yanataka60/X1_SD/JPEG/CZ-800.JPG

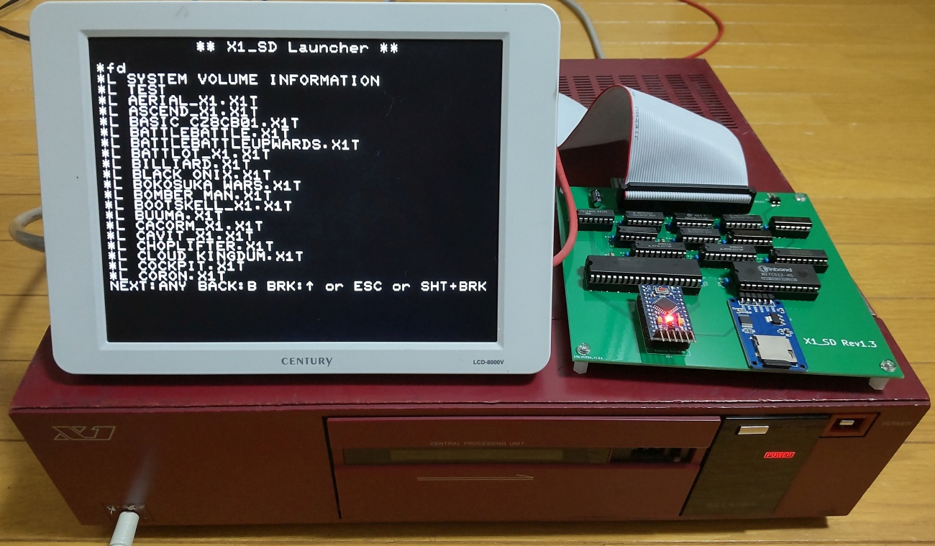
JPEG/CZ-800.JPG
