yanataka60/X1_SD/JPEG/CZ-801.JPG

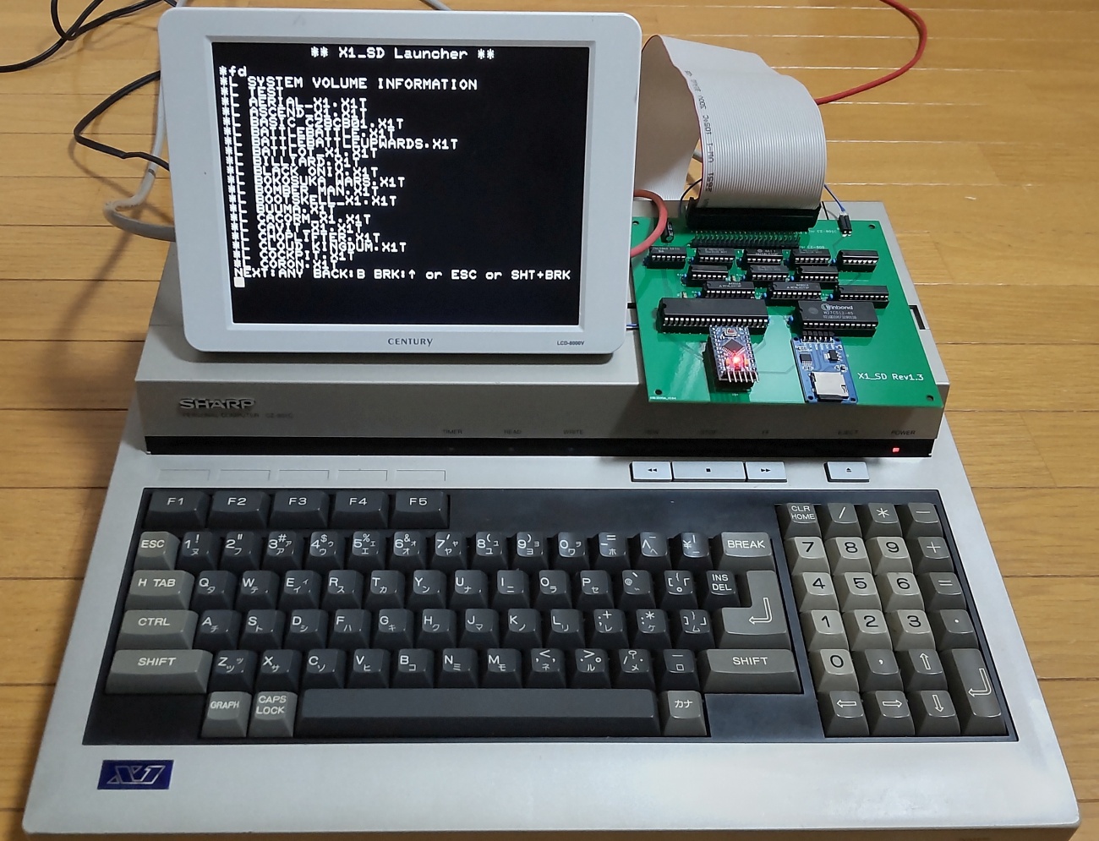
JPEG/CZ-801.JPG
