yanataka60/X1_SD/JPEG/CZ-852.JPG

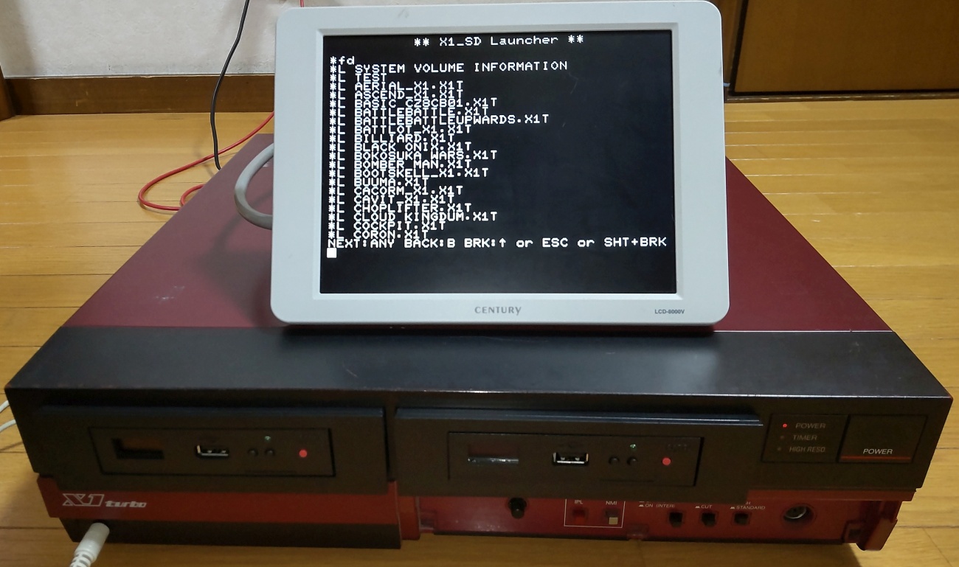
JPEG/CZ-852.JPG
