yanataka60/X1_SD/JPEG/X1_SD.JPG

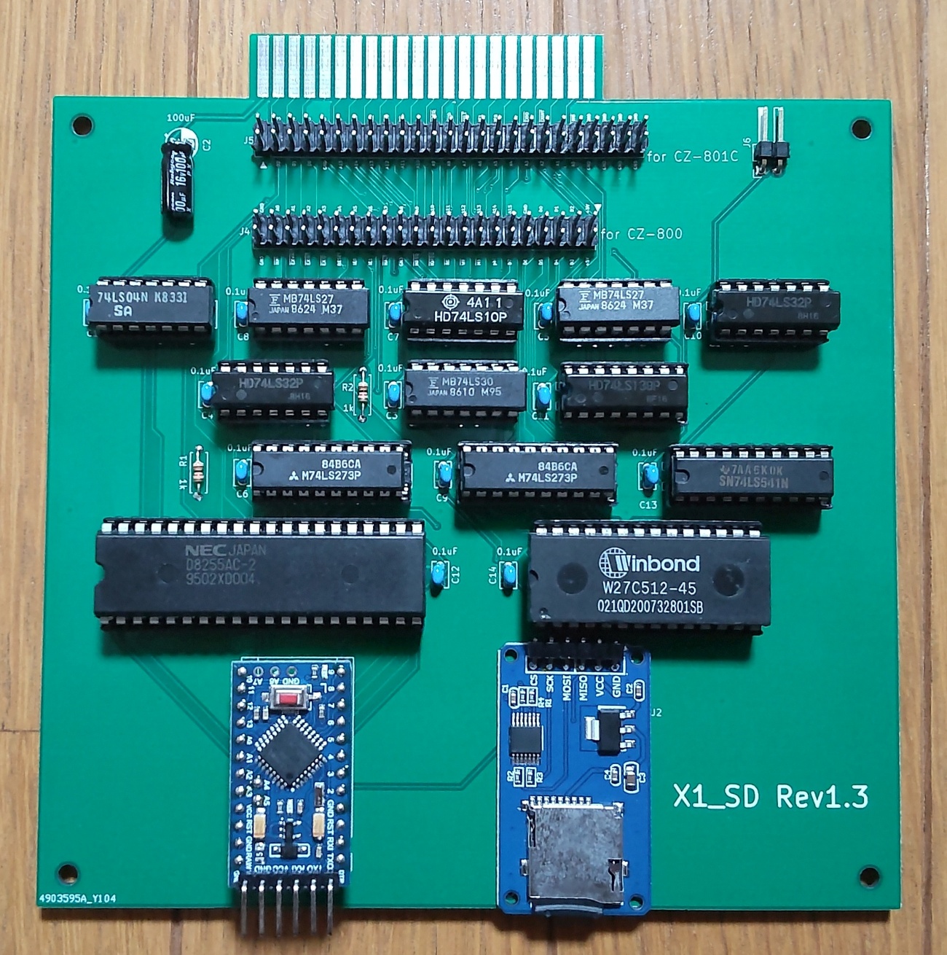
JPEG/X1_SD.JPG
